duststorm24/ChessMaster/data/chess-pieces/board.jpg

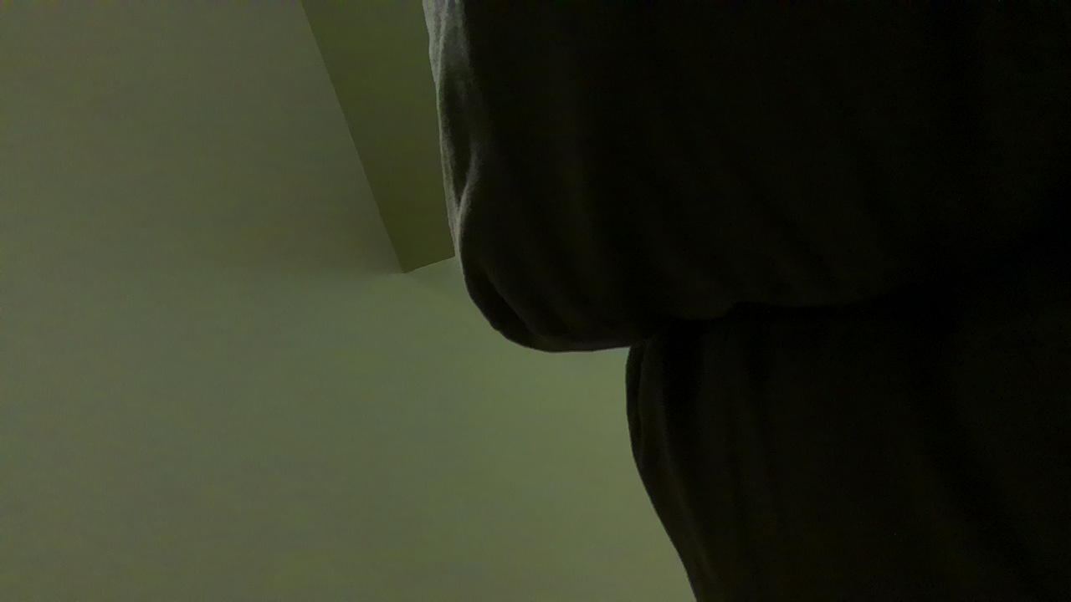
data/chess-pieces/board.jpg
