duststorm24/ChessMaster/hardware/cad/v3-cad-files/Worm Wheel.stl

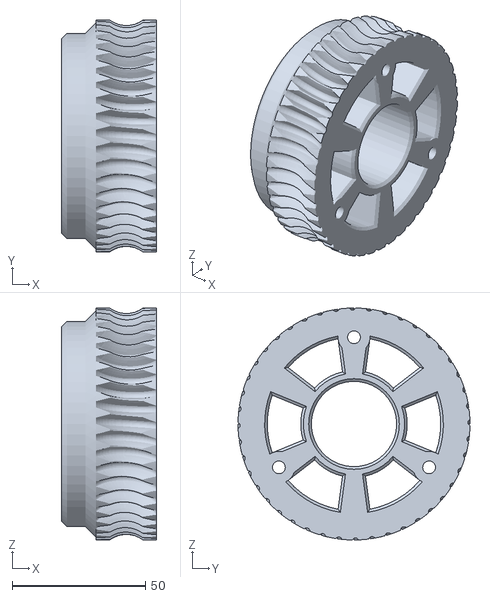
[picture p17: CAD file, 2026-06-21]
hardware/cad/v3-cad-files/Worm Wheel.stl
35.7 x 87.0 x 87.0
