duststorm24/ChessMaster/hardware/cad/v3-cad-files/V4 Base.stl

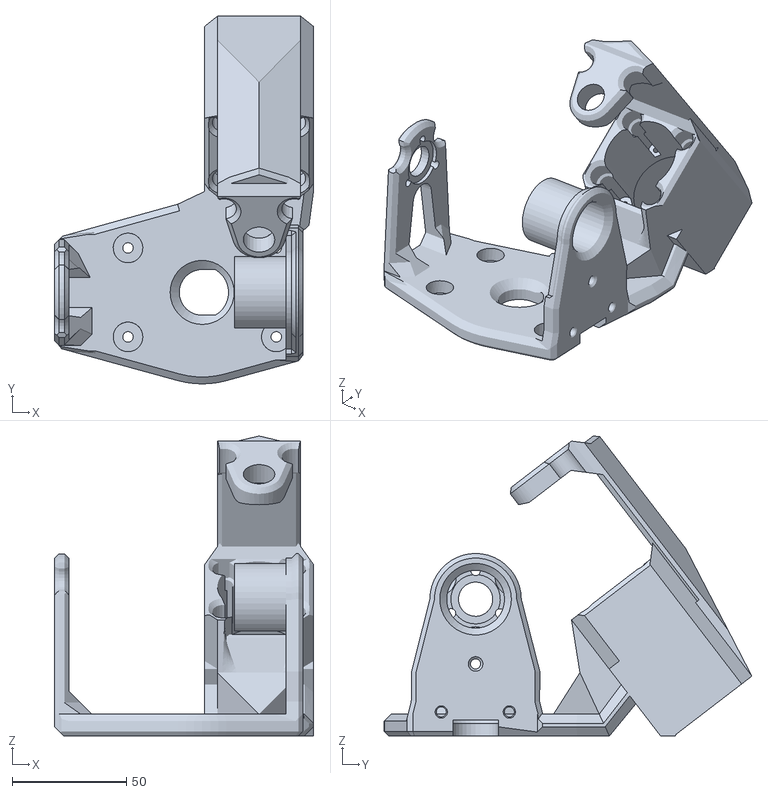
[picture p18: CAD file, 2026-06-21]
hardware/cad/v3-cad-files/V4 Base.stl
113.2 x 160.8 x 131.1
