duststorm24/ChessMaster/hardware/cad/v3-cad-files/Base Plate V3.stl

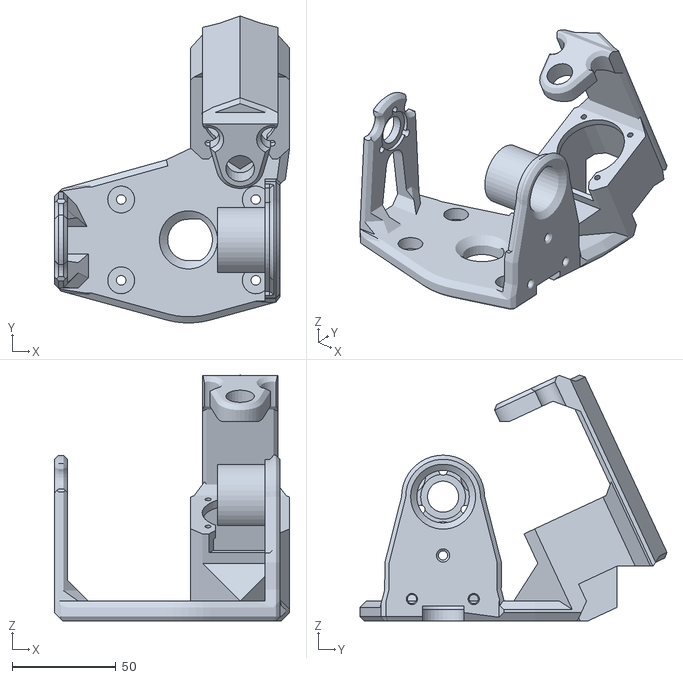
[picture p19: CAD file, 2026-06-21]
hardware/cad/v3-cad-files/Base Plate V3.stl
113.2 x 147.8 x 118.3
