duststorm24/ChessMaster/hardware/cad/v3-cad-files/Large Claw V3.stl

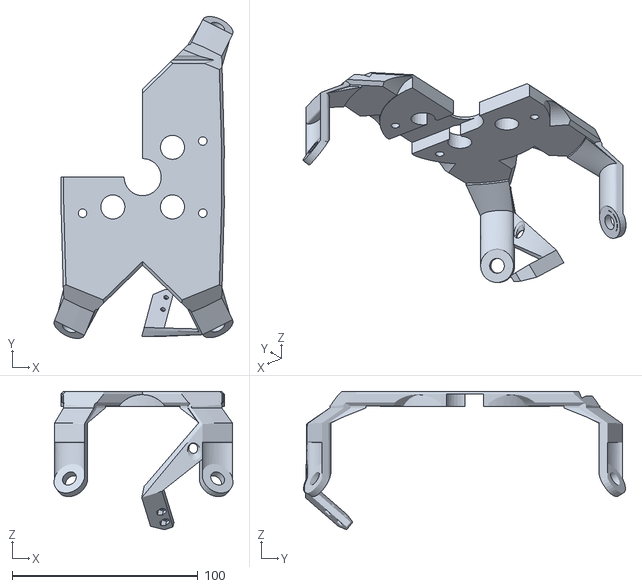
[picture p20: CAD file, 2026-06-21]
hardware/cad/v3-cad-files/Large Claw V3.stl
96.5 x 173.6 x 74.7
