duststorm24/ChessMaster/hardware/cad/v3-cad-files/Arm 1 Worm Gear V3.stl

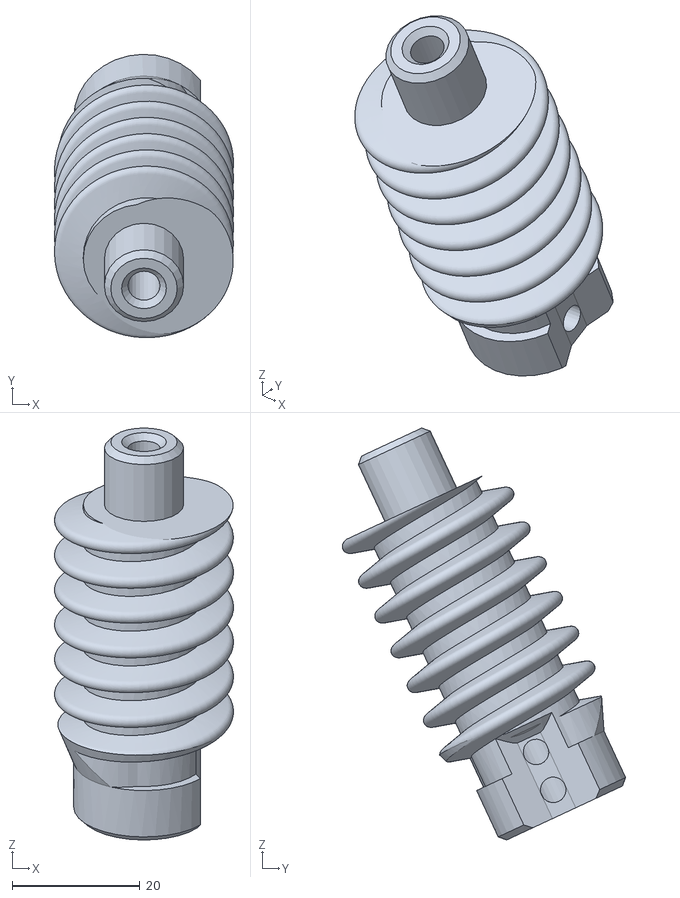
[picture p21: CAD file, 2026-06-21]
hardware/cad/v3-cad-files/Arm 1 Worm Gear V3.stl
28.0 x 44.3 x 64.4
