duststorm24/ChessMaster/hardware/cad/v3-cad-files/Arm 1 Base V3.stl

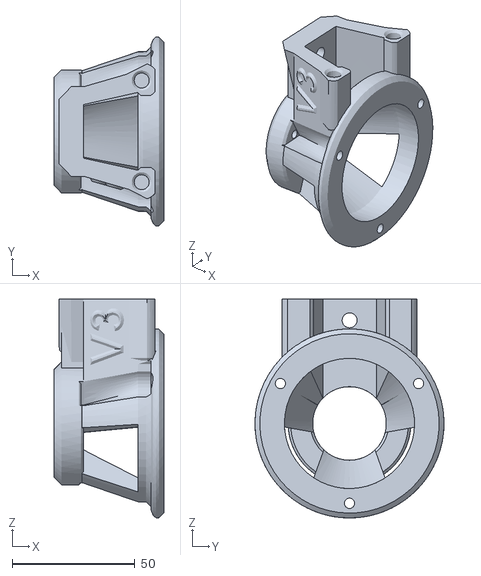
[picture p22: CAD file, 2026-06-21]
hardware/cad/v3-cad-files/Arm 1 Base V3.stl
44.6 x 77.0 x 89.2
