duststorm24/ChessMaster/hardware/cad/v3-cad-files/Arm 1 V4.stl

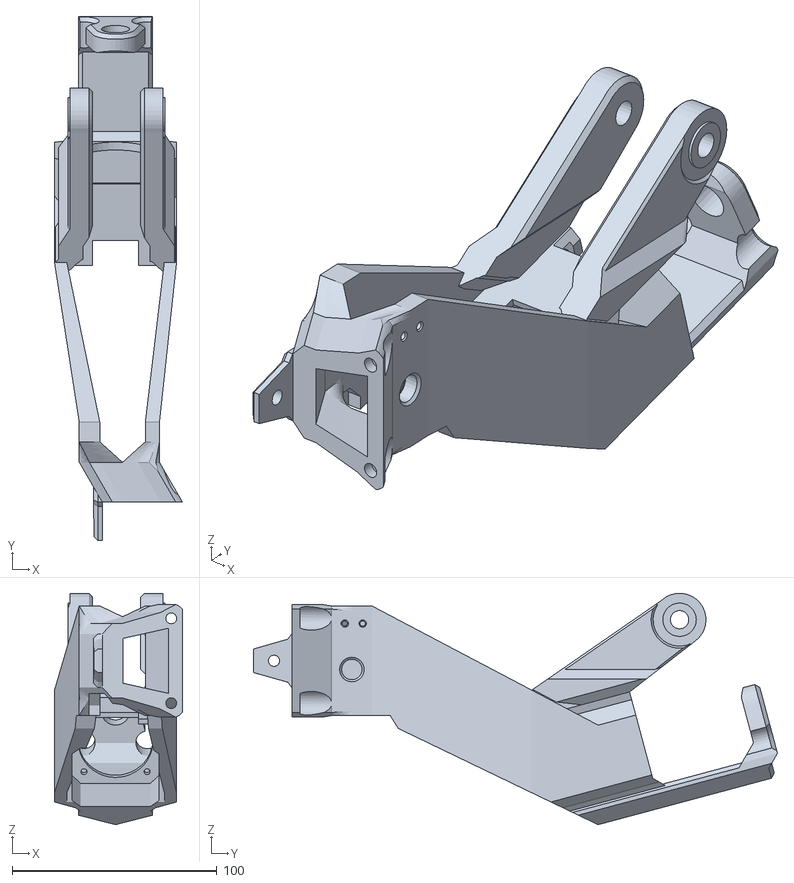
[picture p23: CAD file, 2026-06-21]
hardware/cad/v3-cad-files/Arm 1 V4.stl
62.5 x 255.8 x 113.0
